jo2y/WorkingStargate/Stargate_mk2/rail_l_1_x1.stl

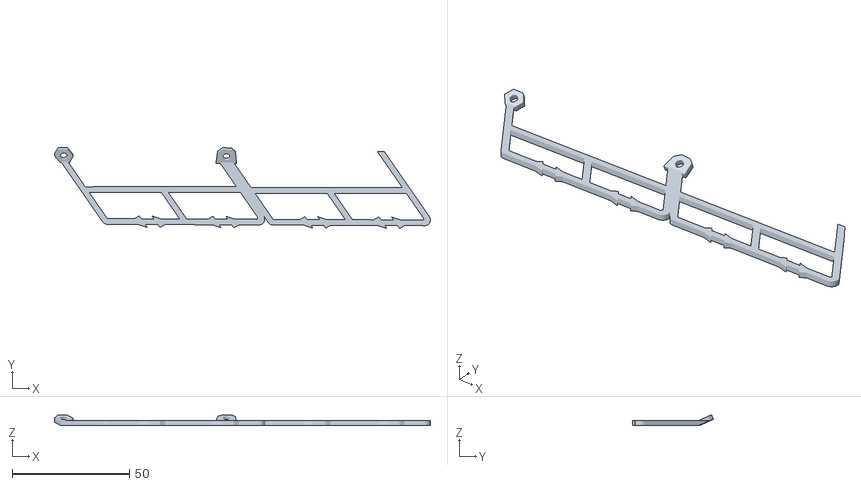
[picture p14: CAD file, 2016-06-05]
Stargate_mk2/rail_l_1_x1.stl
160.2 x 34.5 x 4.49
