jo2y/WorkingStargate/Stargate_mk2/chevron_2_a_x9.stl

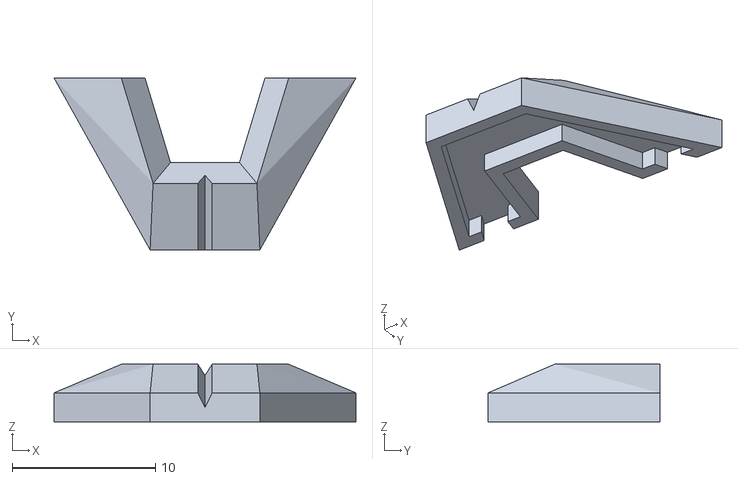
[picture p15: CAD file, 2016-06-05]
Stargate_mk2/chevron_2_a_x9.stl
21.1 x 12.0 x 4.01
