jo2y/WorkingStargate/Stargate_mk2/gear_chevron_x1.stl

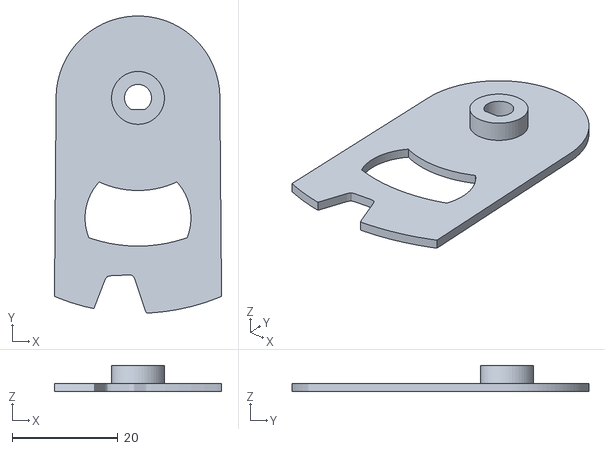
[picture p16: CAD file, 2016-06-05]
Stargate_mk2/gear_chevron_x1.stl
31.6 x 56.1 x 5.00
