jo2y/WorkingStargate/Stargate_mk2/gate_3_d_x1.stl

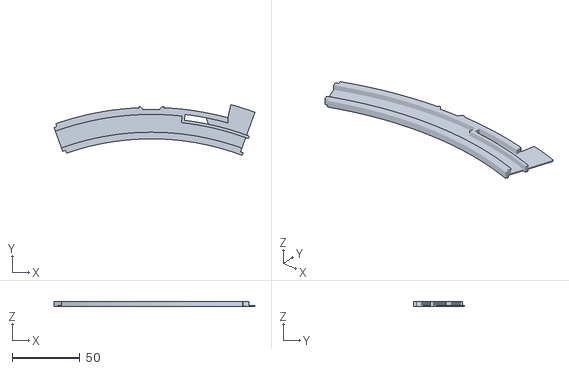
[picture p17: CAD file, 2016-06-05]
Stargate_mk2/gate_3_d_x1.stl
148.6 x 37.6 x 4.00
