jo2y/WorkingStargate/Stargate_mk2/chevron_4_x9.stl

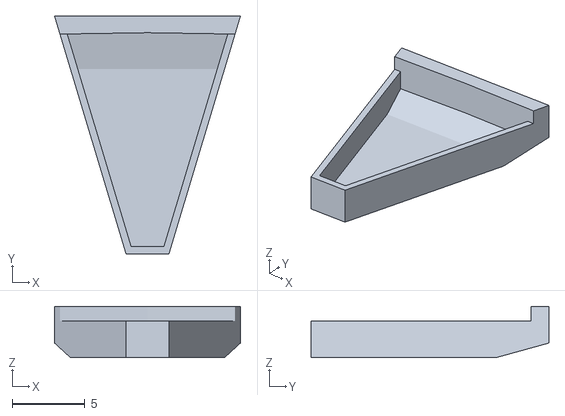
[picture p18: CAD file, 2016-06-05]
Stargate_mk2/chevron_4_x9.stl
12.8 x 16.3 x 3.51
