jo2y/WorkingStargate/Stargate_mk2/ring_2_x6.stl

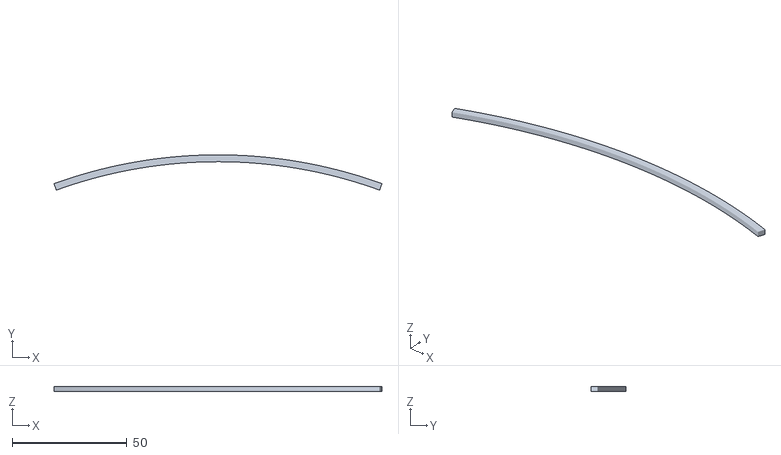
[picture p19: CAD file, 2016-06-05]
Stargate_mk2/ring_2_x6.stl
142.9 x 15.4 x 2.00
