jo2y/WorkingStargate/Stargate_mk2/gate_1_b_x1.stl

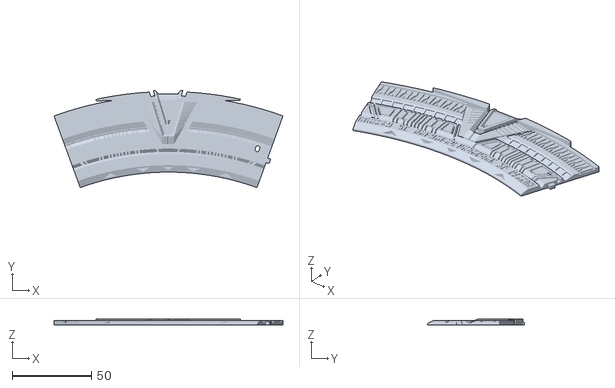
[picture p20: CAD file, 2016-06-05]
Stargate_mk2/gate_1_b_x1.stl
144.1 x 61.2 x 4.01
