jo2y/WorkingStargate/Stargate_mk2/led_x1.stl

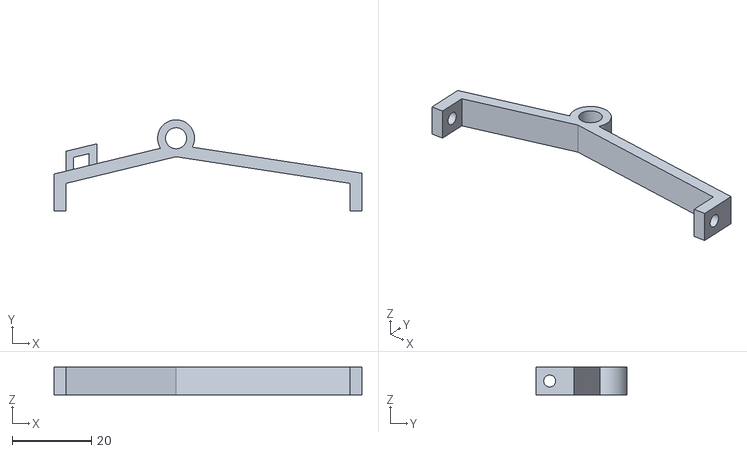
[picture p21: CAD file, 2016-06-05]
Stargate_mk2/led_x1.stl
77.5 x 23.0 x 7.00
