jo2y/WorkingStargate/Stargate_mk2/base_half_front_x1.stl

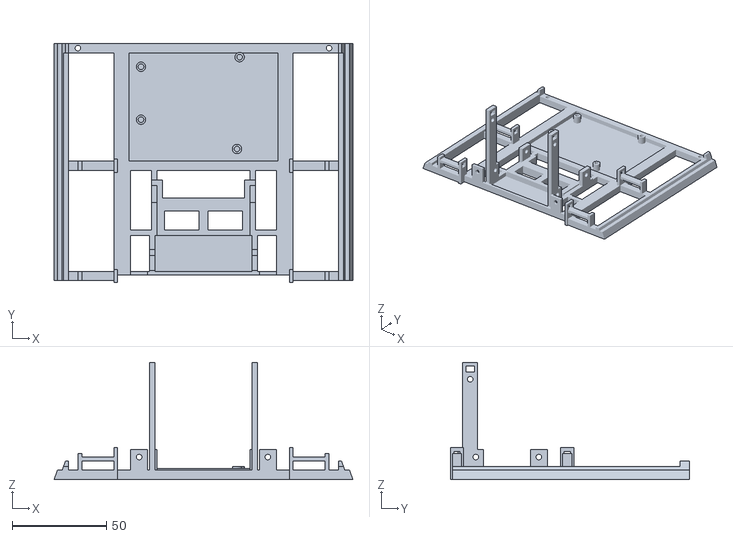
[picture p22: CAD file, 2016-06-05]
Stargate_mk2/base_half_front_x1.stl
158.8 x 127.1 x 62.3
