jo2y/WorkingStargate/Stargate_mk2/ring_1_x1.stl

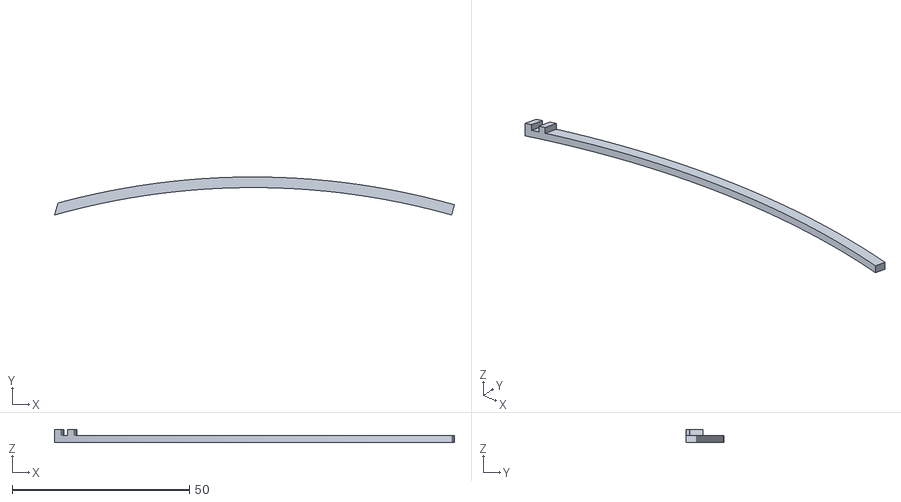
[picture p23: CAD file, 2016-06-05]
Stargate_mk2/ring_1_x1.stl
112.8 x 10.7 x 3.68
