jo2y/WorkingStargate/Stargate_mk2/ldr_x1.stl

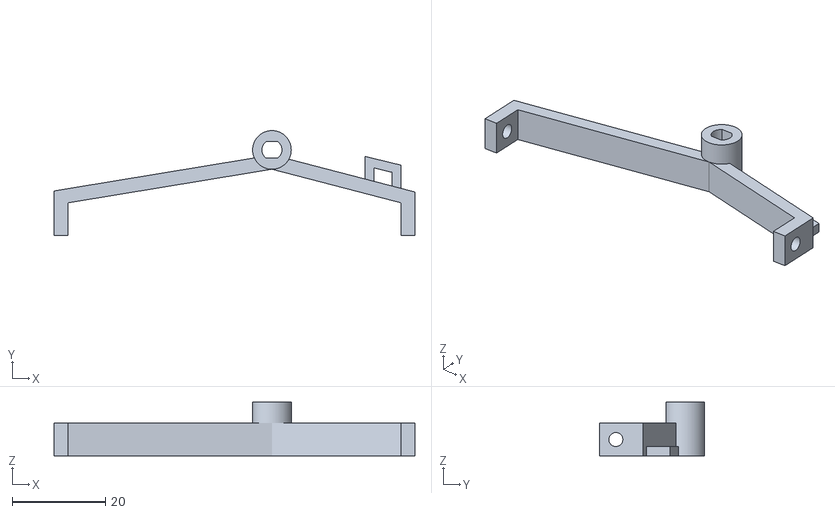
[picture p24: CAD file, 2016-06-05]
Stargate_mk2/ldr_x1.stl
77.5 x 22.5 x 11.5
