jo2y/WorkingStargate/Stargate_mk2/ring_7_x1.stl

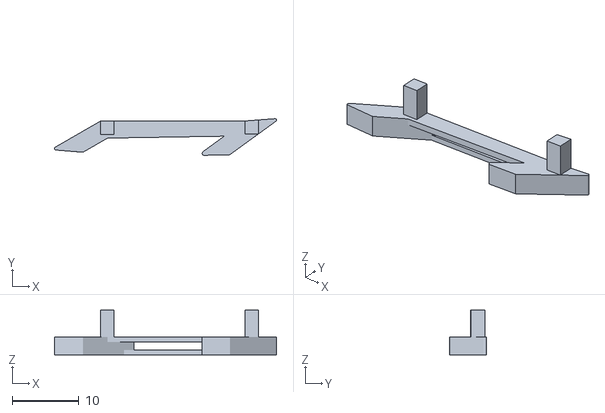
[picture p25: CAD file, 2016-06-05]
Stargate_mk2/ring_7_x1.stl
33.2 x 5.50 x 6.70
