jo2y/WorkingStargate/Stargate_mk2/chevron_2_b_x9.stl

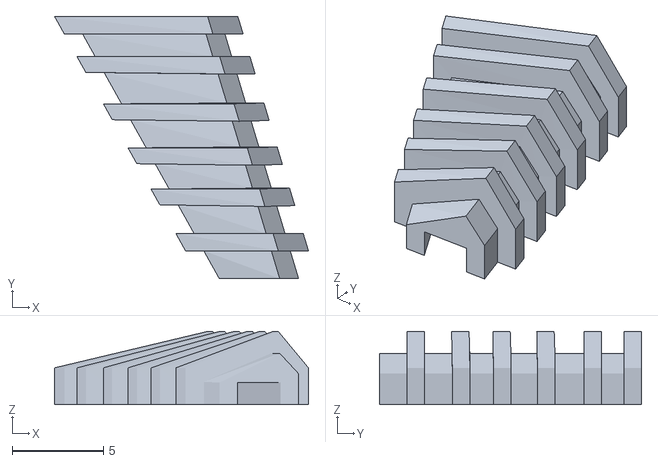
[picture p26: CAD file, 2016-06-05]
Stargate_mk2/chevron_2_b_x9.stl
13.9 x 14.4 x 4.01
