jo2y/WorkingStargate/Stargate_mk2/gate_4_d_x1.stl

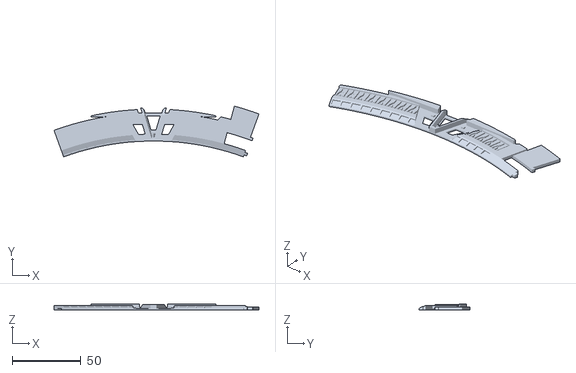
[picture p27: CAD file, 2016-06-05]
Stargate_mk2/gate_4_d_x1.stl
148.9 x 36.8 x 4.01
