jo2y/WorkingStargate/Stargate_mk2/gate_5_x9.stl

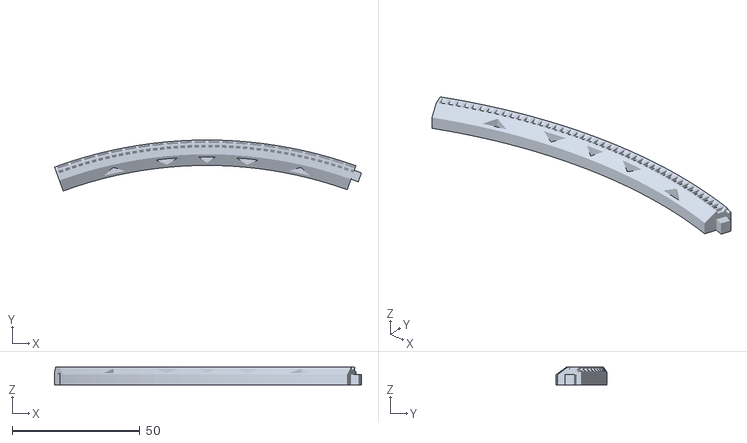
[picture p28: CAD file, 2016-06-05]
Stargate_mk2/gate_5_x9.stl
120.3 x 20.0 x 7.00
