jo2y/WorkingStargate/Stargate_mk2/ramp_3_x1.stl

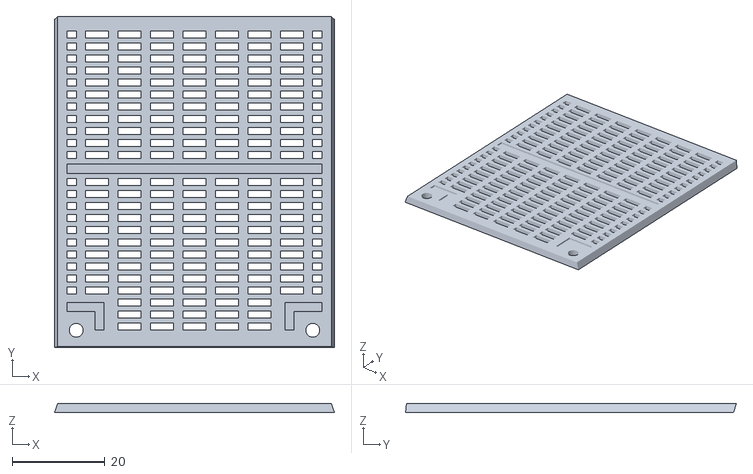
[picture p29: CAD file, 2016-06-05]
Stargate_mk2/ramp_3_x1.stl
60.4 x 71.4 x 2.00
