jo2y/WorkingStargate/Stargate_mk2/ring_6_x1.stl

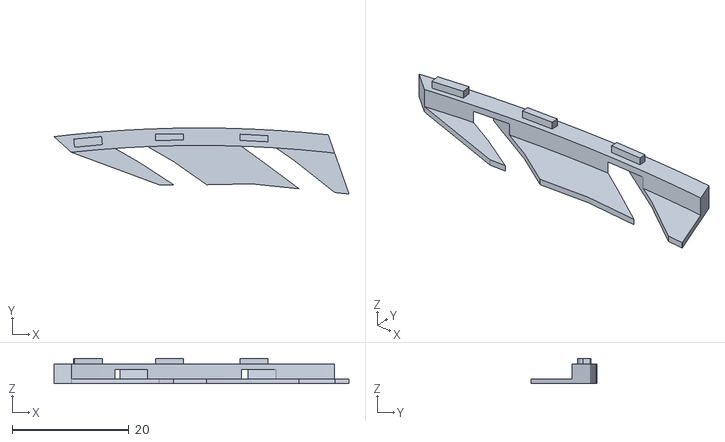
[picture p30: CAD file, 2016-06-05]
Stargate_mk2/ring_6_x1.stl
50.5 x 11.3 x 4.34
