jo2y/WorkingStargate/Stargate_mk2/gate_4_b_x6.stl

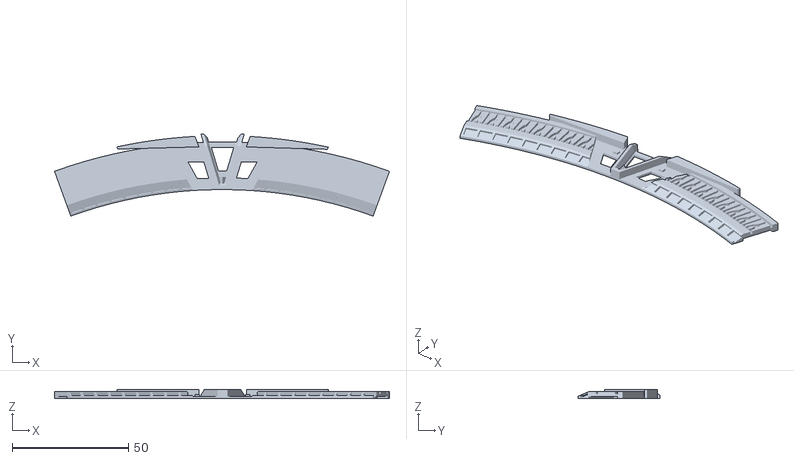
[picture p31: CAD file, 2016-06-05]
Stargate_mk2/gate_4_b_x6.stl
144.1 x 35.4 x 4.01
