jo2y/WorkingStargate/Stargate_mk2/base_rear_x1.stl

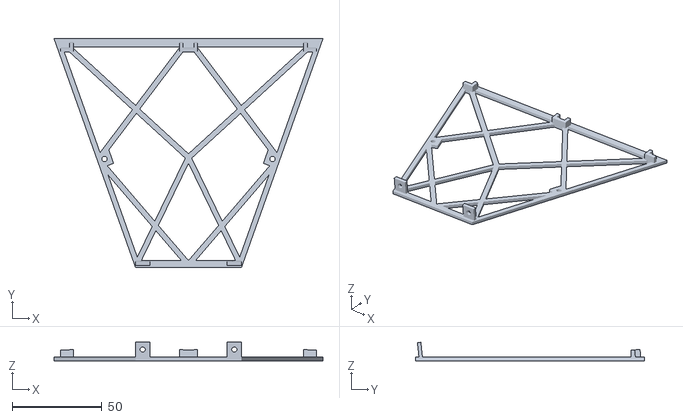
[picture p32: CAD file, 2016-06-05]
Stargate_mk2/base_rear_x1.stl
149.9 x 127.8 x 10.4
