jo2y/WorkingStargate/Stargate_mk2/rail_r_1_x1.stl

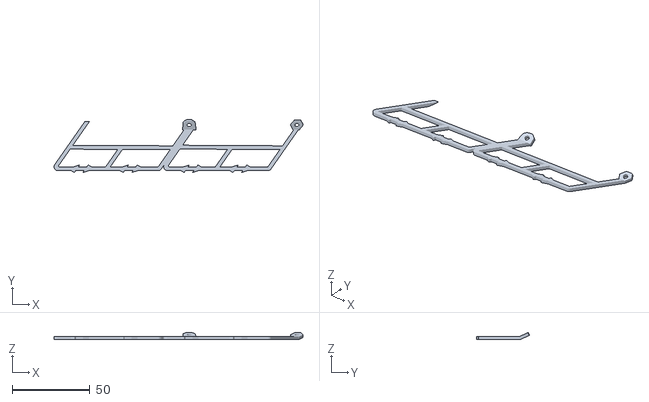
[picture p33: CAD file, 2016-06-05]
Stargate_mk2/rail_r_1_x1.stl
160.3 x 34.2 x 4.49
