jo2y/WorkingStargate/Stargate_mk2/symbol_5_x1.stl

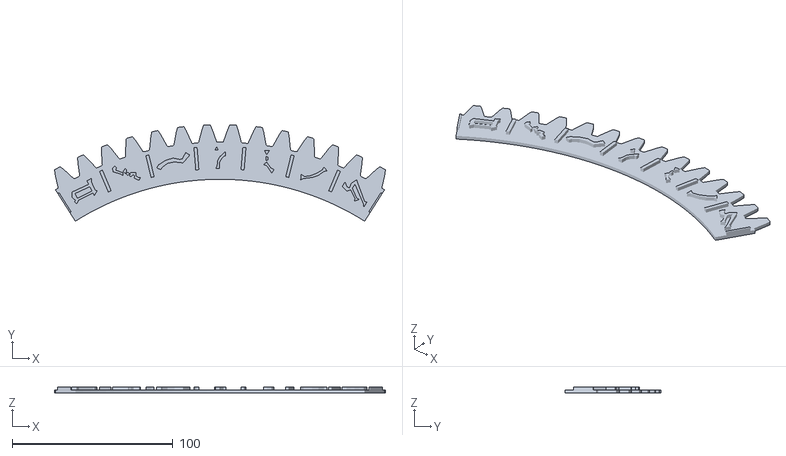
[picture p34: CAD file, 2016-06-05]
Stargate_mk2/symbol_5_x1.stl
206.2 x 60.1 x 4.00
