jo2y/WorkingStargate/Stargate_mk2/gate_3_b_x6.stl

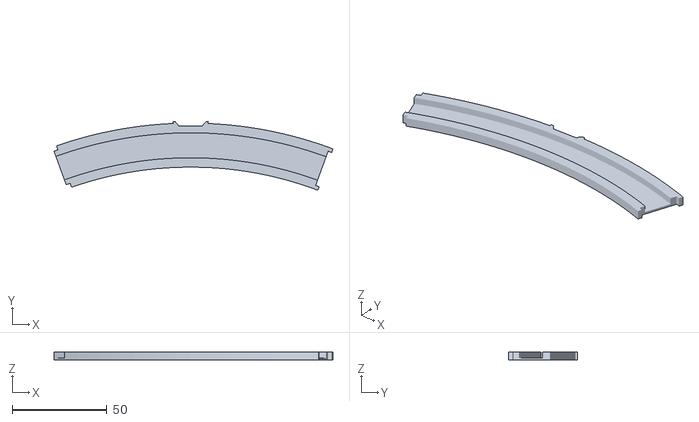
[picture p35: CAD file, 2016-06-05]
Stargate_mk2/gate_3_b_x6.stl
147.0 x 36.1 x 4.00
