jo2y/WorkingStargate/Stargate_mk2/chevron_3_a_x9.stl

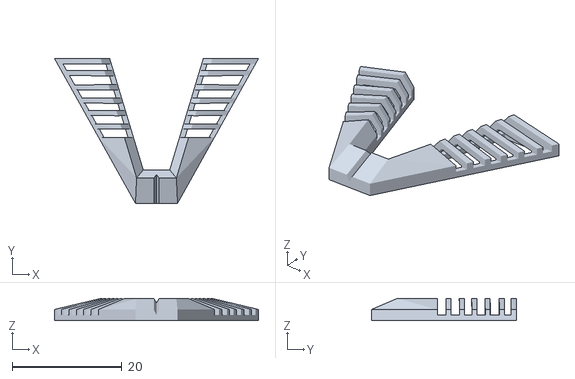
[picture p37: CAD file, 2016-06-05]
Stargate_mk2/chevron_3_a_x9.stl
37.2 x 26.4 x 4.01
