jo2y/WorkingStargate/Stargate_mk2/stepper_mount_x2.stl

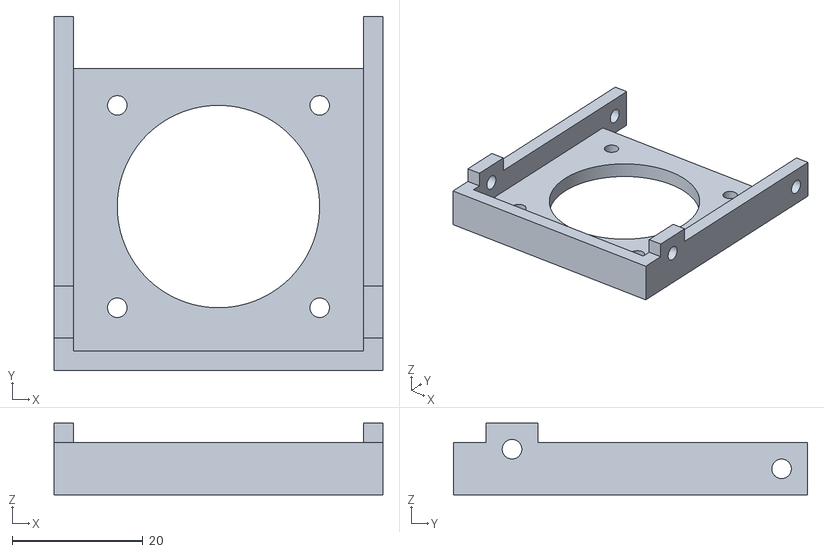
[picture p38: CAD file, 2016-06-05]
Stargate_mk2/stepper_mount_x2.stl
50.4 x 54.3 x 11.0
