jo2y/WorkingStargate/Stargate_mk2/gear_symbol_x1.stl

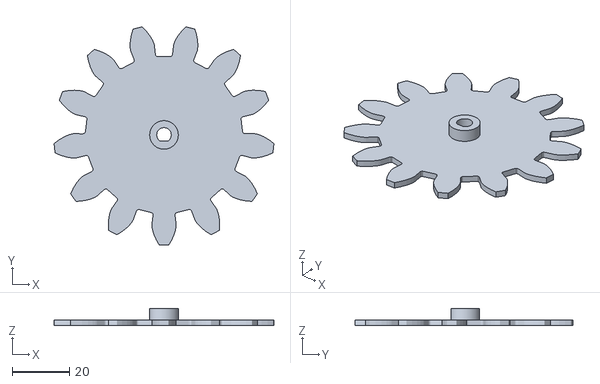
[picture p39: CAD file, 2016-06-05]
Stargate_mk2/gear_symbol_x1.stl
77.0 x 76.5 x 6.00
