jo2y/WorkingStargate/Stargate_mk2/chevron_3_c_x9.stl

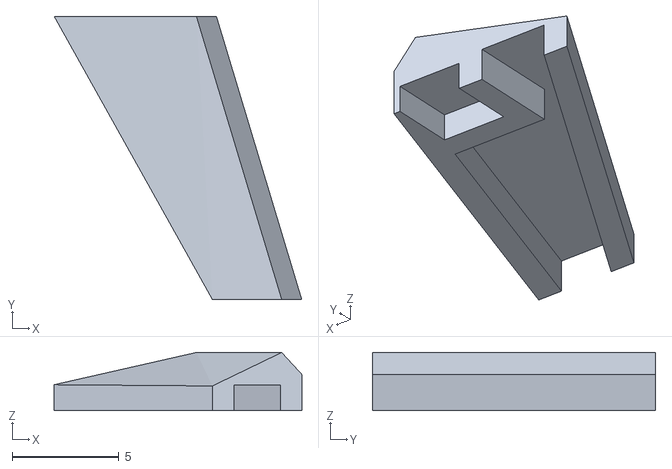
[picture p40: CAD file, 2016-06-05]
Stargate_mk2/chevron_3_c_x9.stl
11.6 x 13.2 x 2.71
