jo2y/WorkingStargate/Stargate_mk2/gate_2_a_x8.stl

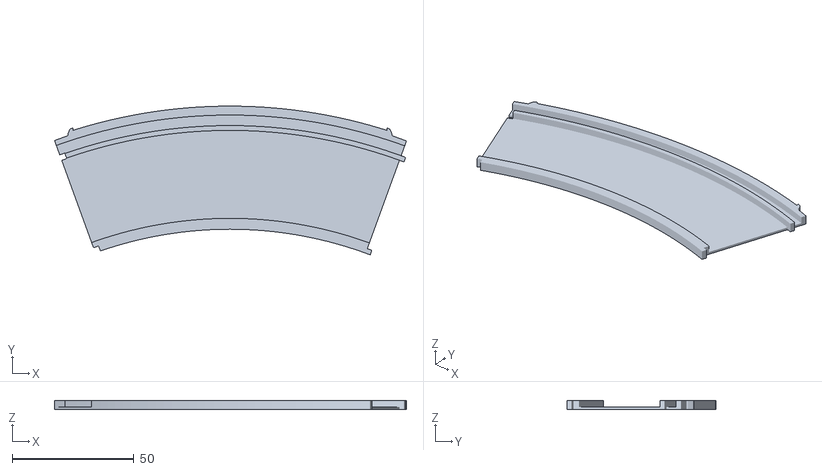
[picture p41: CAD file, 2016-06-05]
Stargate_mk2/gate_2_a_x8.stl
144.9 x 61.2 x 3.64
