jo2y/WorkingStargate/Stargate_mk2/gate_4_a_x1.stl

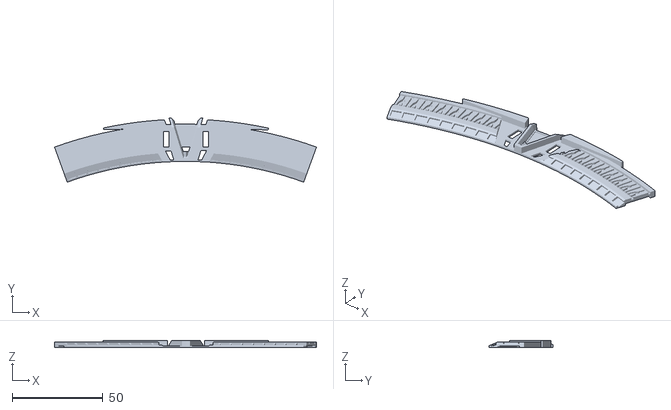
[picture p42: CAD file, 2016-06-05]
Stargate_mk2/gate_4_a_x1.stl
144.1 x 35.4 x 4.01
