jo2y/WorkingStargate/Stargate_mk2/ramp_1_x1.stl

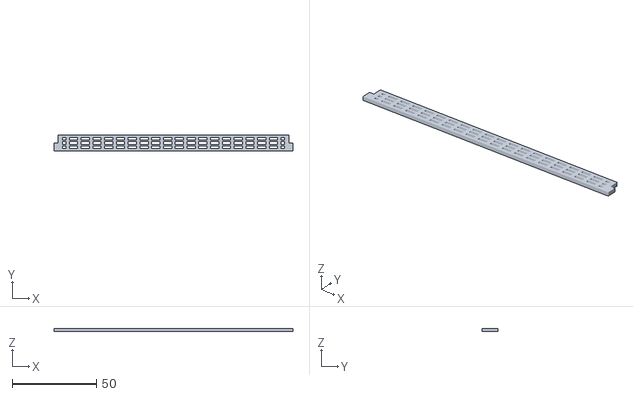
[picture p43: CAD file, 2016-06-05]
Stargate_mk2/ramp_1_x1.stl
142.2 x 9.69 x 2.00
