jo2y/WorkingStargate/Stargate_mk2/base_l_1_x1.stl

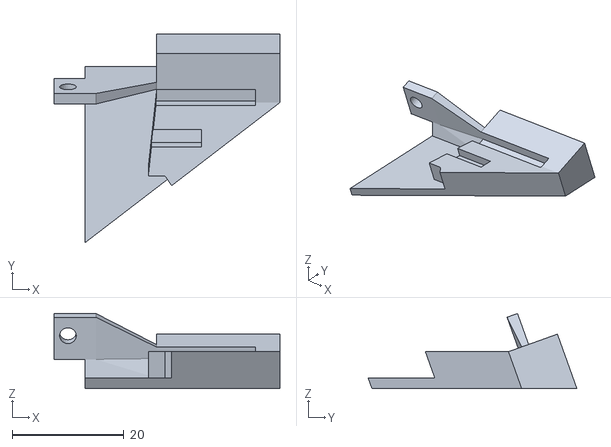
[picture p44: CAD file, 2016-06-05]
Stargate_mk2/base_l_1_x1.stl
40.4 x 37.4 x 13.4
