jo2y/WorkingStargate/Stargate_mk2/rail_r_3_x4.stl

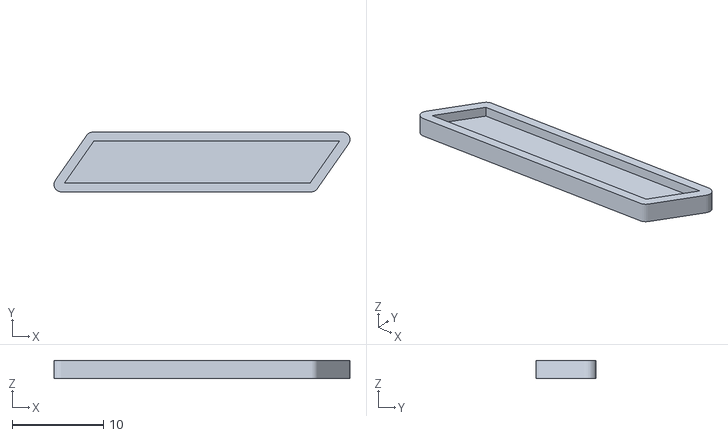
[picture p45: CAD file, 2016-06-05]
Stargate_mk2/rail_r_3_x4.stl
32.4 x 6.56 x 2.00
