jo2y/WorkingStargate/Stargate_mk2/gate_3_a_x1.stl

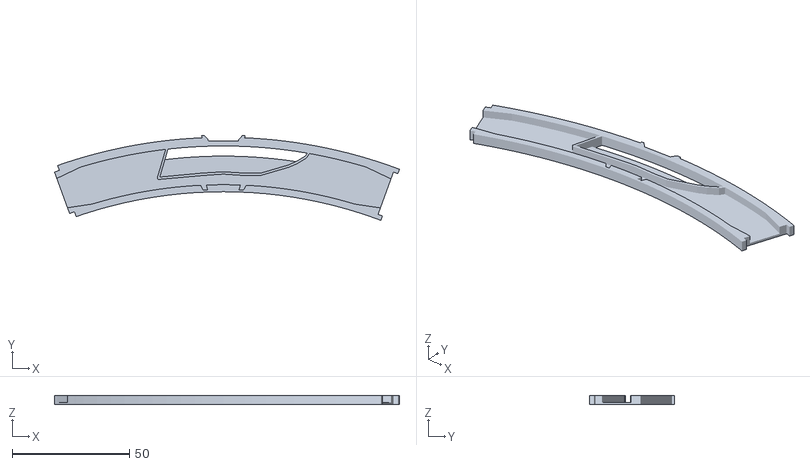
[picture p46: CAD file, 2016-06-05]
Stargate_mk2/gate_3_a_x1.stl
147.0 x 36.1 x 4.00
