jo2y/WorkingStargate/Stargate_mk2/gate_2_b_x1.stl

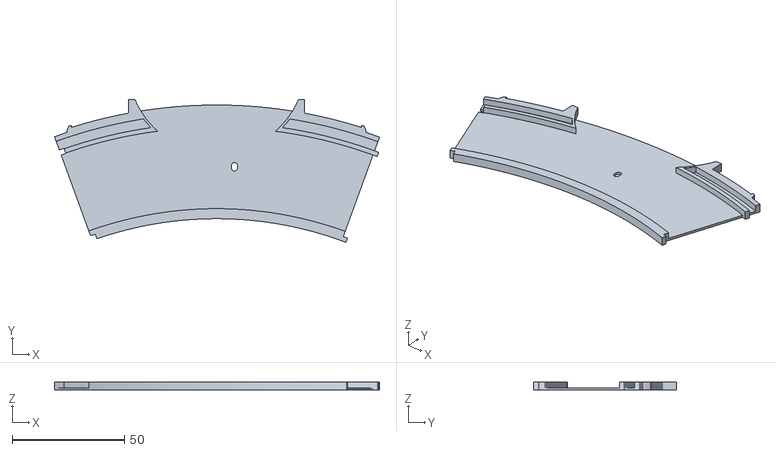
[picture p47: CAD file, 2016-06-05]
Stargate_mk2/gate_2_b_x1.stl
144.9 x 63.6 x 3.64
