jo2y/WorkingStargate/Stargate_mk2/base_half_back_x1.stl

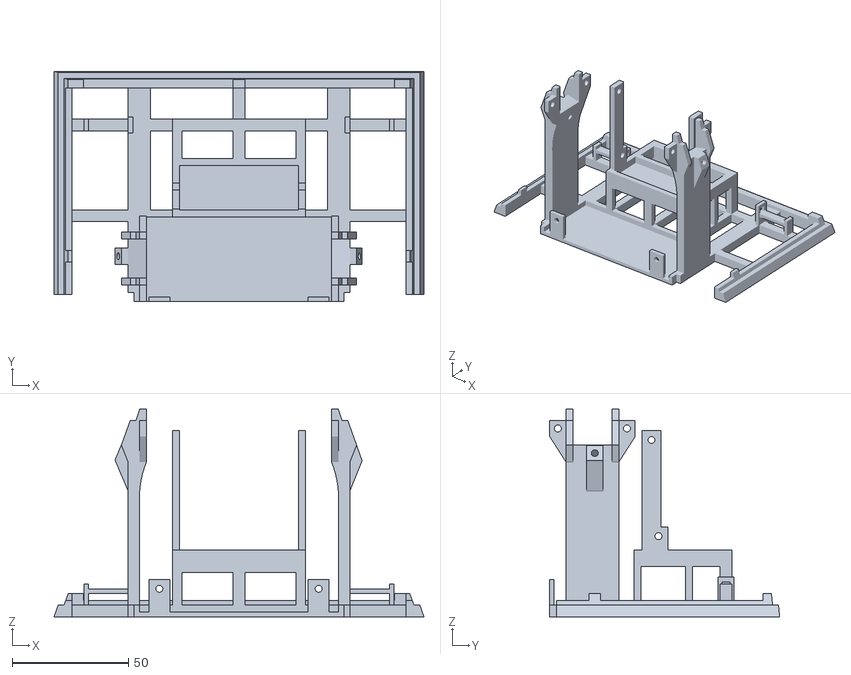
[picture p48: CAD file, 2016-06-05]
Stargate_mk2/base_half_back_x1.stl
158.8 x 98.9 x 89.1
