jo2y/WorkingStargate/Stargate_mk2/ring_5_x1.stl

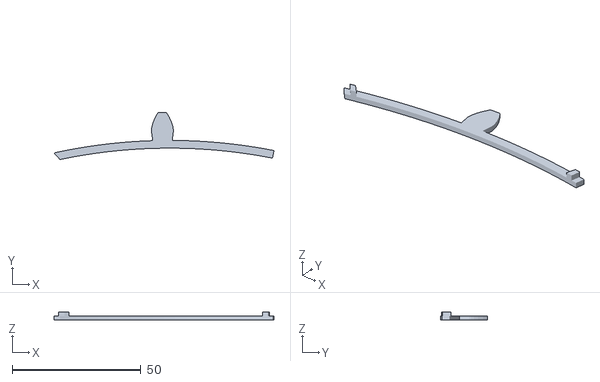
[picture p49: CAD file, 2016-06-05]
Stargate_mk2/ring_5_x1.stl
85.3 x 18.3 x 3.24
