jo2y/WorkingStargate/Stargate_mk2/gate_4_c_x1.stl

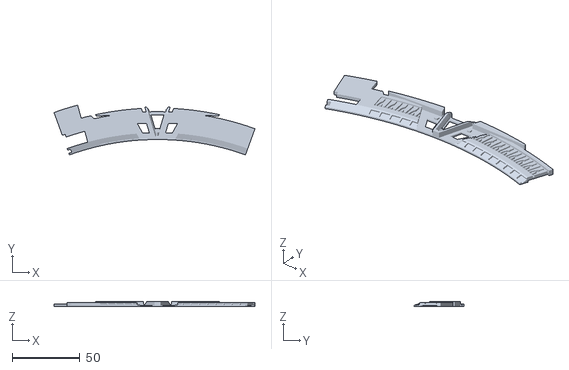
[picture p50: CAD file, 2016-06-05]
Stargate_mk2/gate_4_c_x1.stl
147.9 x 36.7 x 4.01
