jo2y/WorkingStargate/Stargate_mk2/ramp_2_x1.stl

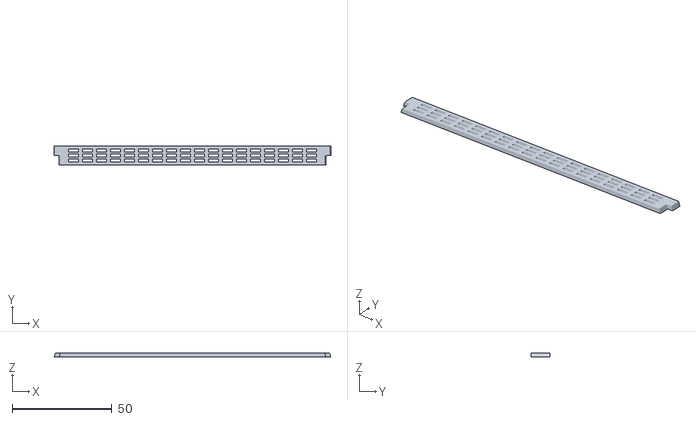
[picture p51: CAD file, 2016-06-05]
Stargate_mk2/ramp_2_x1.stl
138.6 x 9.69 x 2.00
